lambdamikel/picoram6116/pics/6116-mpf-1b-c.jpg

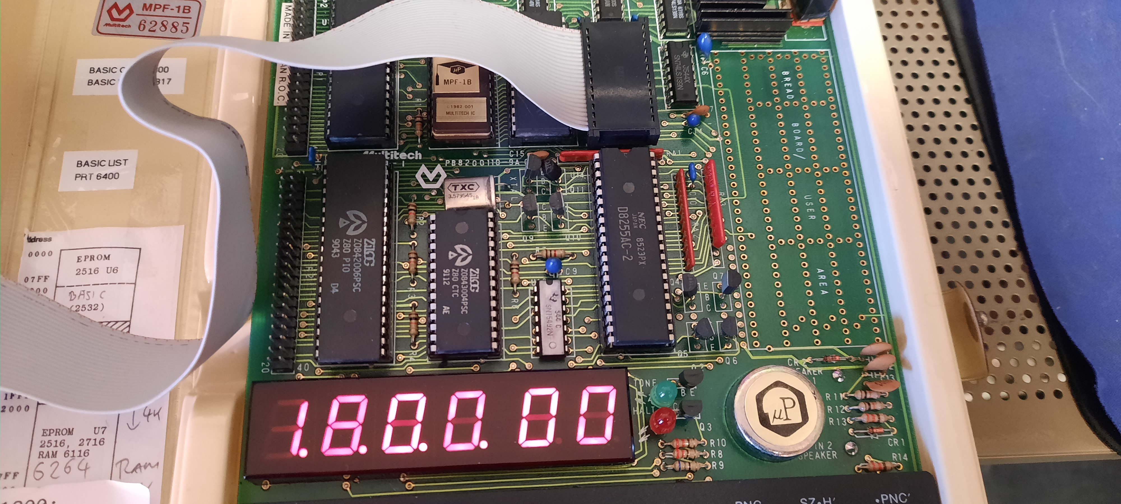
pics/6116-mpf-1b-c.jpg
